KrasForge/Courant/hardware/courant/deliverables/courant-netlist.txt

Current repaired native board: courant.kicad_pcb
102 nets

A3V3 (6)
    C160.1
    C161.1
    C162.1
    R120.2
    U3.1
    U3.8

CLK100_RAW (2)
    R114.1
    Y1.3

DAC_CAPM (2)
    C163.2
    U3.4

DAC_CAPP (2)
    C163.1
    U3.2

DAC_L (2)
    R126.1
    U3.6

DAC_LDO (2)
    C165.1
    U3.18

DAC_R (2)
    R127.1
    U3.7

DAC_VNEG (2)
    C164.1
    U3.5

DONE (2)
    R101.1
    U1.122

ENC_A_RAW (2)
    J18.4
    R140.1

ENC_B_RAW (2)
    J18.5
    R141.1

ENC_SW_RAW (2)
    J18.6
    R142.1

FB1 (3)
    R10.2
    R11.1
    U11.5

FB2 (3)
    R20.2
    R21.1
    U12.5

FB3 (3)
    R30.2
    R31.1
    U13.5

FLASH_CLK (2)
    R110.2
    U2.6

FLASH_CLK_RAW (2)
    R110.1
    U1.72

FLASH_CS (3)
    R111.1
    U1.172
    U2.1

FLASH_HOLD (3)
    R113.1
    U1.160
    U2.7

FLASH_MISO (2)
    U1.142
    U2.2

FLASH_MOSI (2)
    U1.141
    U2.5

FLASH_WP (3)
    R112.1
    U1.159
    U2.3

GATE_DIV (5)
    C196.1
    D12.3
    R166.2
    R167.1
    U7.3

GATE_IN (2)
    J17.15
    R166.1

GATE_REF (3)
    R168.2
    R169.1
    U7.4

GND (190)
    C1.2
    C10.2
    C100.2
    C101.2
    C102.2
    C103.2
    C104.2
    C105.2
    C106.2
    C107.2
    C108.2
    C109.2
    C11.2
    C110.2
    C111.2
    C112.2
    C113.2
    C114.2
    C115.2
    C116.2
    C117.2
    C118.2
    C119.2
    C12.2
    C120.2
    C121.2
    C122.2
    C123.2
    C124.2
    C125.2
    C126.2
    C127.2
    C128.2
    C129.2
    C13.2
    C130.2
    C131.2
    C132.2
    C133.2
    C134.2
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
    R142.2
    R145.1
    U1.8

gate (2)
    U1.10
    U7.1

led0 (2)
    R147.1
    U1.12

led1 (2)
    R148.1
    U1.28

led2 (2)
    R149.1
    U1.13

led3 (2)
    R150.1
    U1.14

midi_rx (3)
    R181.1
    U1.25
    U8.4

reset_n (5)
    C146.1
    J18.16
    J4.1
    R106.1
    U1.26
