KrasForge/Courant/src/tb/mesh_resonator_tb.vhd

-------------------------------------------------------------------------------
-- mesh_resonator_tb.vhd  -  oversampling + decimation path validation
--
-- Drives a 9x9 mesh_resonator at OS = 4 with a hard centred impulse and checks
-- the decimated audio-rate output bit-for-bit against the reference model
-- (model/ os_gen: oversampled non-linear mesh + boxcar decimation) over 256
-- audio frames. Coefficients are precomputed for the oversampled rate
-- (gamma2 = (c*(k/4)/h)^2, etc.).
--
-- The companion study (model/ os_gen) measures the aliasing reduction: spectral
-- SNR vs a 16x ground truth rises monotonically with the oversampling factor
-- (1x: -8.7 dB, 2x: -5.0, 4x: 0.3, 8x: 10.0), i.e. measurable aliasing
-- reduction vs 1x.
--
-- Golden trace: src/tb/os_trace.txt  ("out_l" per frame).
--
-- VHDL-2008.
-------------------------------------------------------------------------------

library ieee;
use ieee.std_logic_1164.all;
use ieee.numeric_std.all;
use std.textio.all;
use std.env.all;

library work;
use work.fdtd_pkg.all;

entity mesh_resonator_tb is
end entity mesh_resonator_tb;

architecture sim of mesh_resonator_tb is

  constant CLK_PERIOD : time     := 10 ns;
  constant NX         : positive := 9;
  constant NY         : positive := 9;
  constant OS         : positive := 4;
  constant FRAMES     : positive := 256;

  signal clk    : std_logic := '0';
  signal rst    : std_logic := '1';
  signal frame  : std_logic := '0';
  signal coeffs : coeffs_t;
  signal exc_in : q123_t := (others => '0');
  signal exc_en : std_logic := '0';
  signal out_l  : q123_t;
  signal out_r  : q123_t;
  signal ovalid : std_logic;

  signal done : boolean := false;
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
